DisDis/article-dslideshow/images/v7/Power_PCB.png

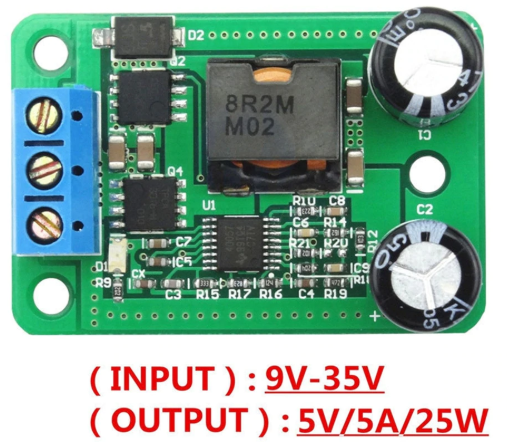
images/v7/Power_PCB.png
