DisDis/article-dslideshow/images/v7/USB_C_1.png

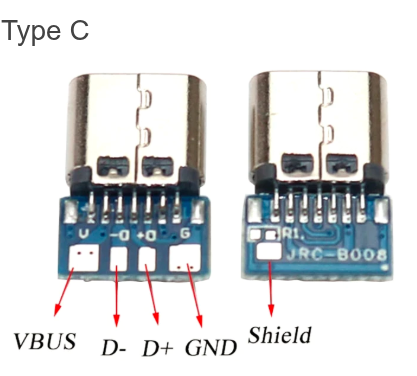
images/v7/USB_C_1.png
